open-ephys/shuttle-drive/large_64drives/assembly-jig/50mm_4mm_dowel.SLDPRT

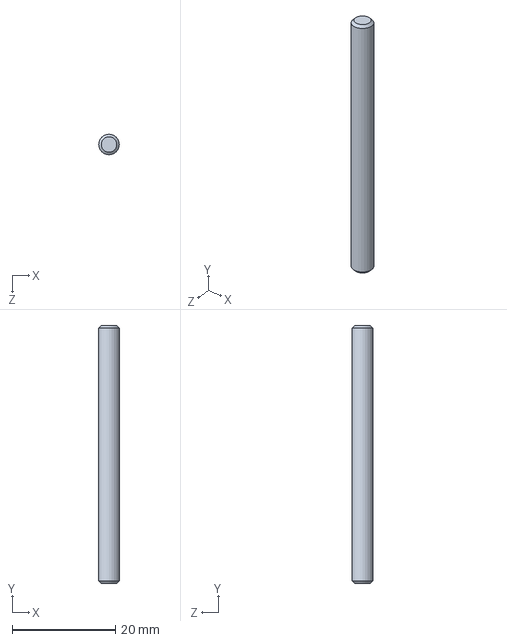
[picture p17: CAD file, 2019-11-18]
large_64drives/assembly-jig/50mm_4mm_dowel.SLDPRT
4.00 x 50.0 x 4.00 mm
