open-ephys/shuttle-drive/large_64drives/CONSMA001-ND.SLDPRT

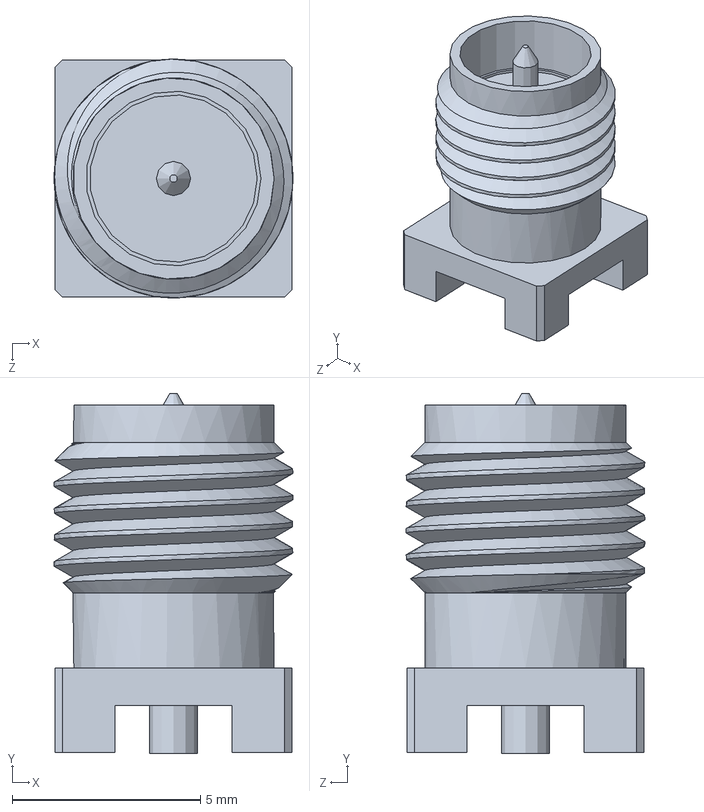
[picture p18: CAD file, 2019-09-19]
large_64drives/CONSMA001-ND.SLDPRT
6.35 x 9.57 x 6.35 mm
