open-ephys/shuttle-drive/small_16drives/assembly_jig/stl_order/low_jig_base_big_rat.STL

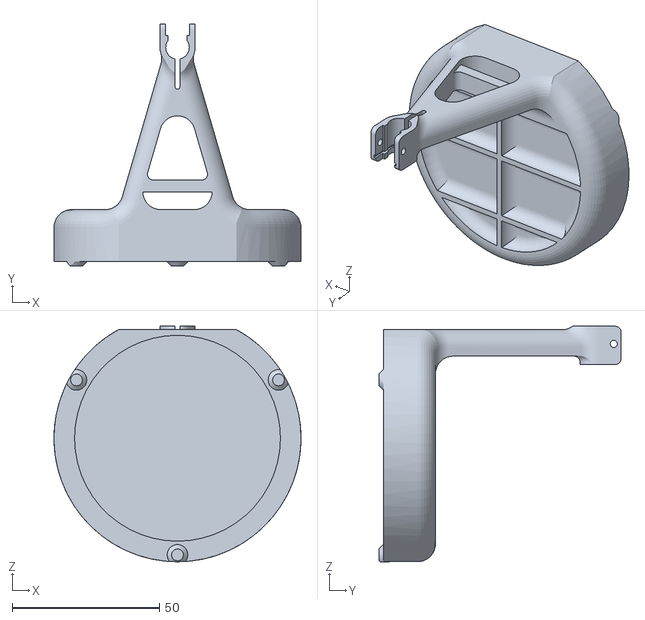
[picture p19: CAD file, 2019-08-24]
small_16drives/assembly_jig/stl_order/low_jig_base_big_rat.STL
83.8 x 82.2 x 79.9
