open-ephys/shuttle-drive/small_16drives/drive_small/drive_shuttle_palletized.SLDPRT

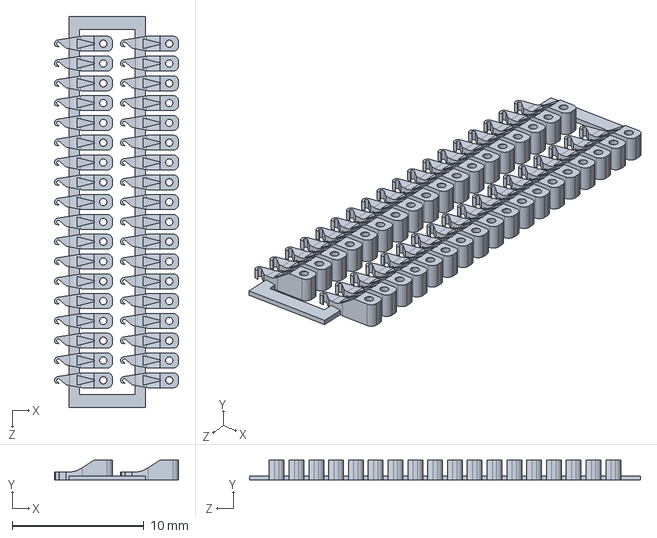
[picture p20: CAD file, 2019-08-24]
small_16drives/drive_small/drive_shuttle_palletized.SLDPRT
9.39 x 1.50 x 29.6 mm
