open-ephys/shuttle-drive/small_16drives/drive_small/not_needed_for_drives/3d_printed_guide_array.SLDPRT

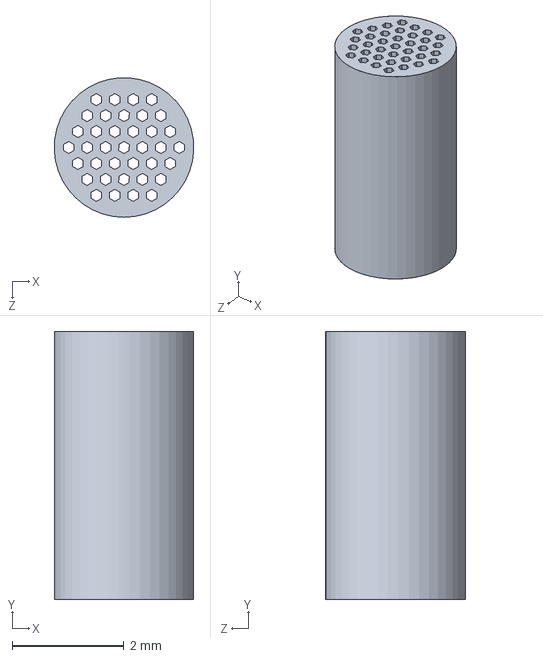
[picture p21: CAD file, 2019-08-24]
small_16drives/drive_small/not_needed_for_drives/3d_printed_guide_array.SLDPRT
2.50 x 4.80 x 2.50 mm
