open-ephys/shuttle-drive/large_64drives/assembly-jig/jig_base_big_rat.SLDPRT

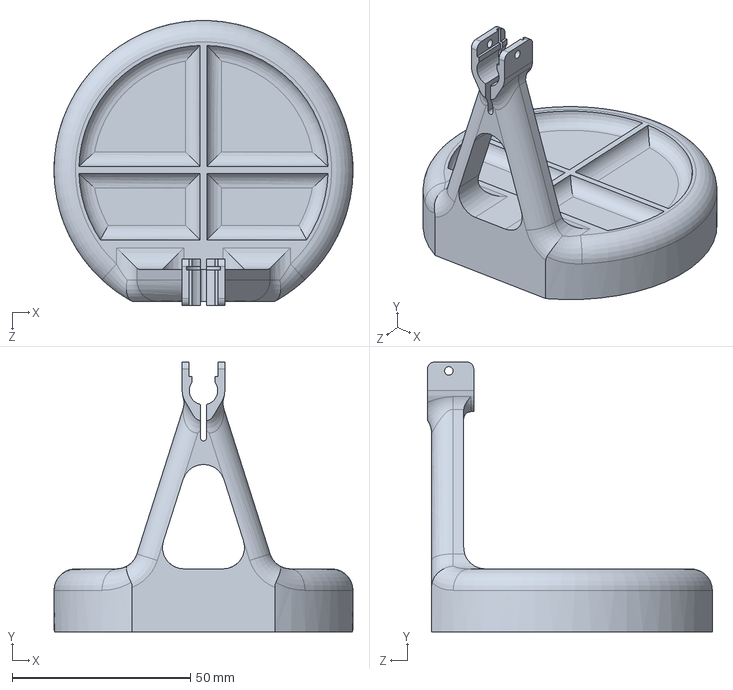
[picture p22: CAD file, 2019-11-18]
large_64drives/assembly-jig/jig_base_big_rat.SLDPRT
83.8 x 75.7 x 79.9 mm
