open-ephys/shuttle-drive/large_64drives/rat_drive_shuttle_short_palletized.SLDPRT

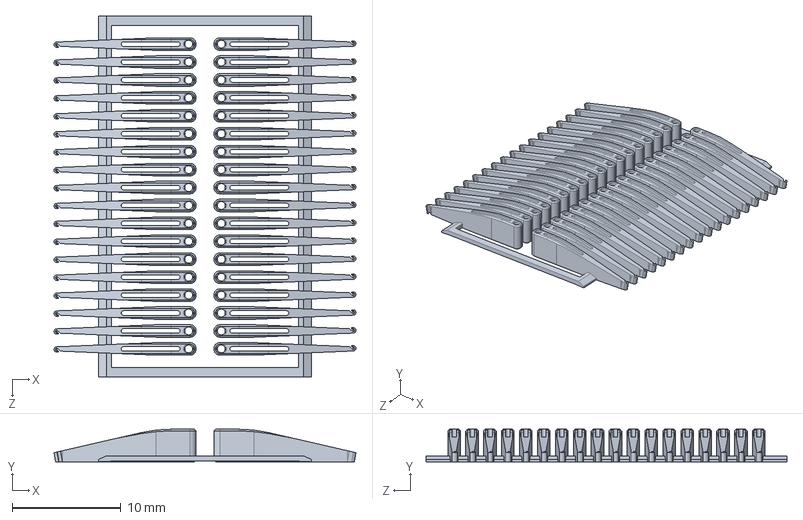
[picture p23: CAD file, 2019-09-19]
large_64drives/rat_drive_shuttle_short_palletized.SLDPRT
27.8 x 3.00 x 33.2 mm
