open-ephys/shuttle-drive/large_64drives/rat_headstage-retainer.sldprt

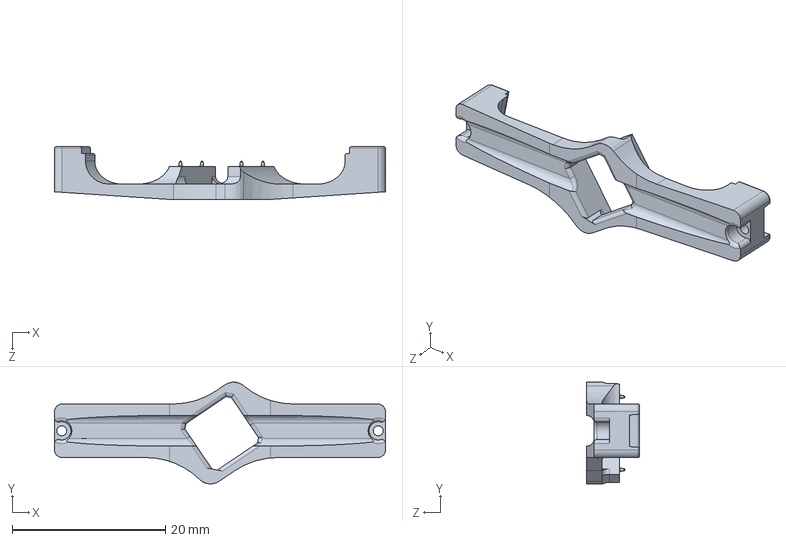
[picture p24: CAD file, 2019-09-19]
large_64drives/rat_headstage-retainer.sldprt
43.2 x 13.3 x 6.90 mm
