open-ephys/shuttle-drive/small_16drives/assembly_jig/stl_order/high_eib_holder_top.STL

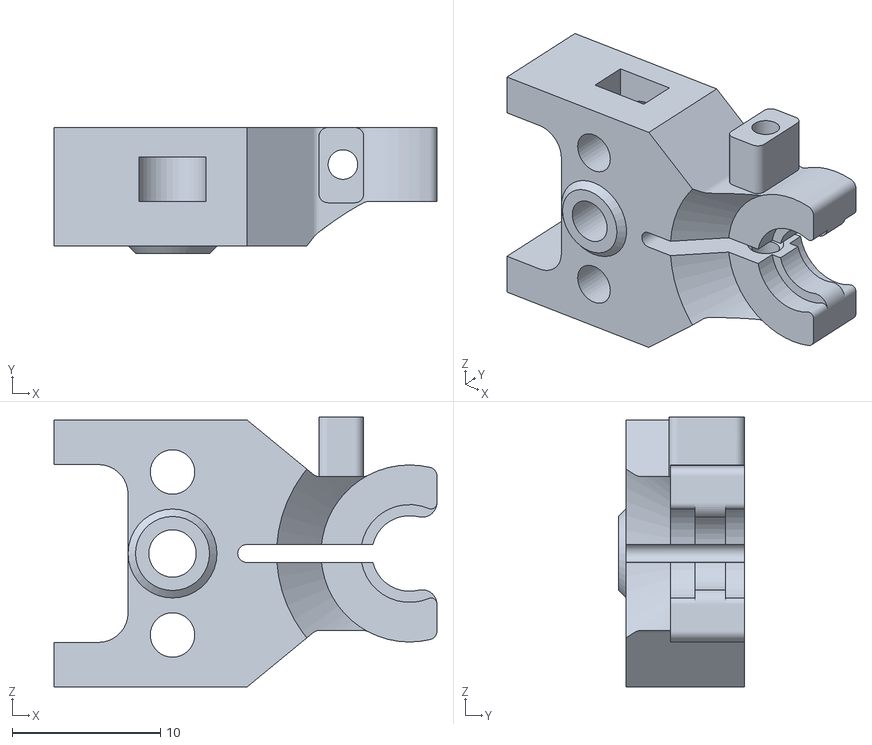
[picture p25: CAD file, 2019-08-24]
small_16drives/assembly_jig/stl_order/high_eib_holder_top.STL
25.9 x 8.50 x 18.2
