open-ephys/shuttle-drive/large_64drives/rat_shuttle_drive_insert_bilateral_vta.SLDPRT

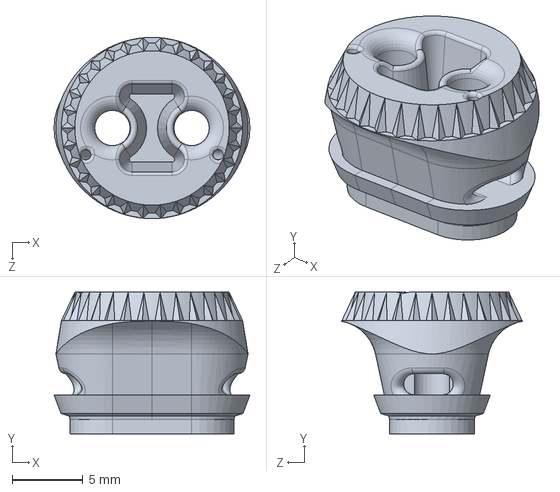
[picture p26: CAD file, 2019-09-19]
large_64drives/rat_shuttle_drive_insert_bilateral_vta.SLDPRT
13.8 x 10.0 x 12.8 mm
