open-ephys/shuttle-drive/small_16drives/assembly_jig/stl_order/high_drive_holder_inner.STL

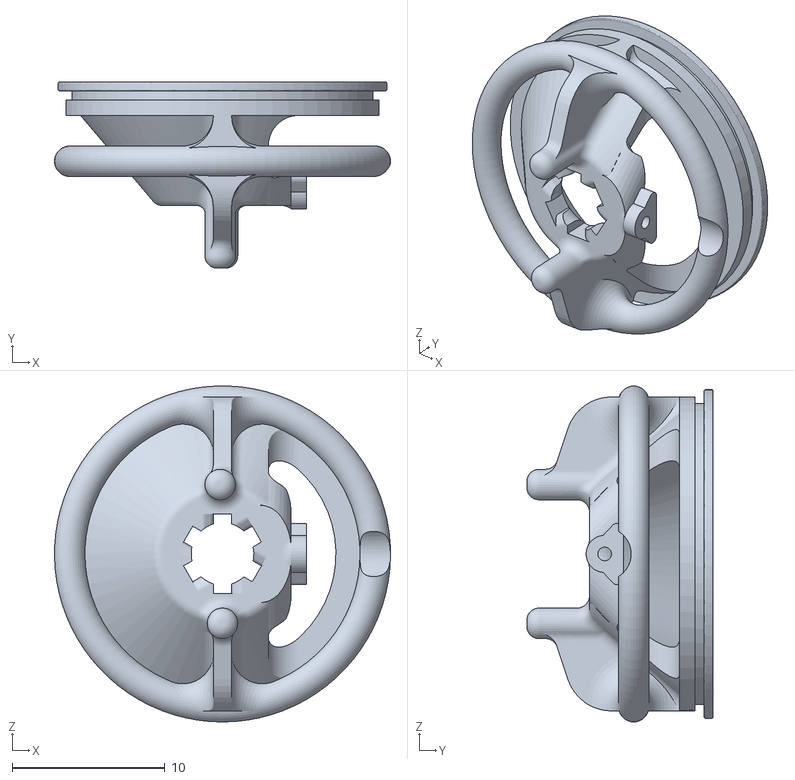
[picture p27: CAD file, 2019-08-24]
small_16drives/assembly_jig/stl_order/high_drive_holder_inner.STL
22.0 x 12.2 x 22.0
