open-ephys/shuttle-drive/large_64drives/rat-eib.SLDPRT

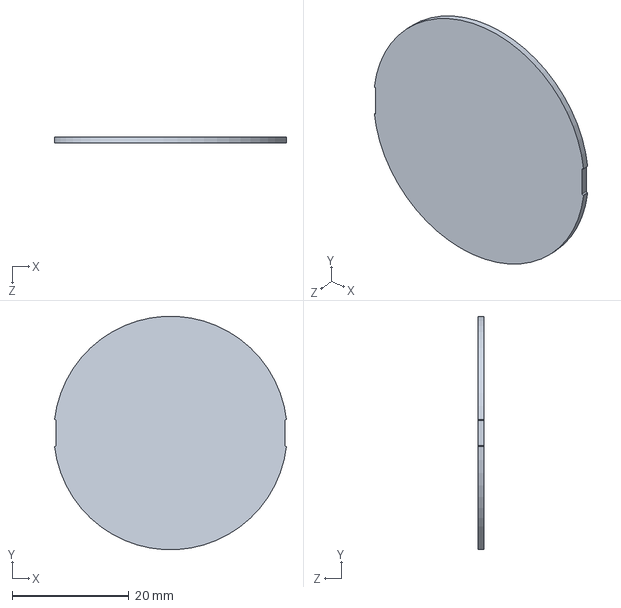
[picture p28: CAD file, 2019-09-19]
large_64drives/rat-eib.SLDPRT
39.7 x 39.9 x 1.00 mm
