open-ephys/shuttle-drive/small_16drives/assembly_jig/stl_order/high_eib_holder_inner_two_omnetics.STL

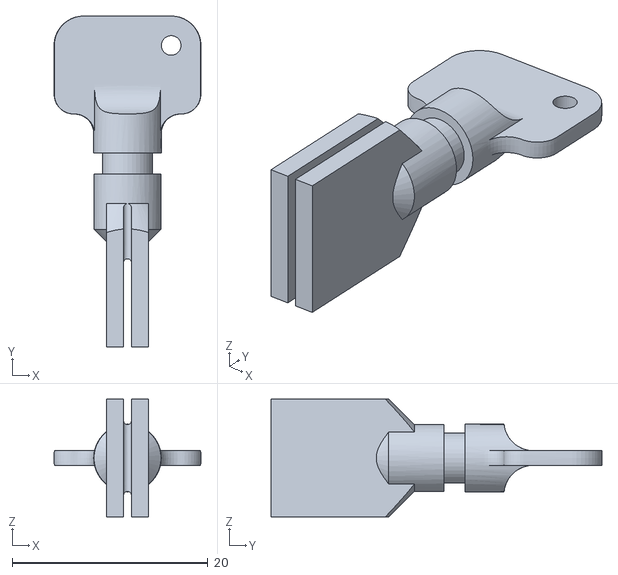
[picture p29: CAD file, 2019-08-24]
small_16drives/assembly_jig/stl_order/high_eib_holder_inner_two_omnetics.STL
15.0 x 33.8 x 12.0
