open-ephys/shuttle-drive/large_64drives/assembly-jig/eib_holder_top.SLDPRT

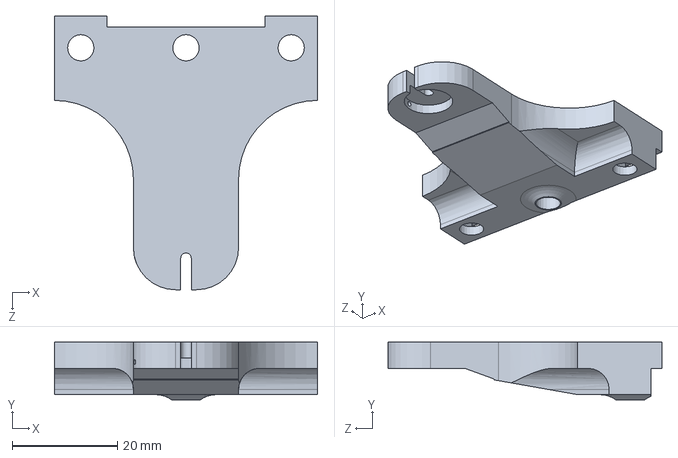
[picture p30: CAD file, 2019-11-18]
large_64drives/assembly-jig/eib_holder_top.SLDPRT
50.0 x 11.0 x 52.0 mm
