open-ephys/shuttle-drive/large_64drives/rat-headstage.SLDPRT

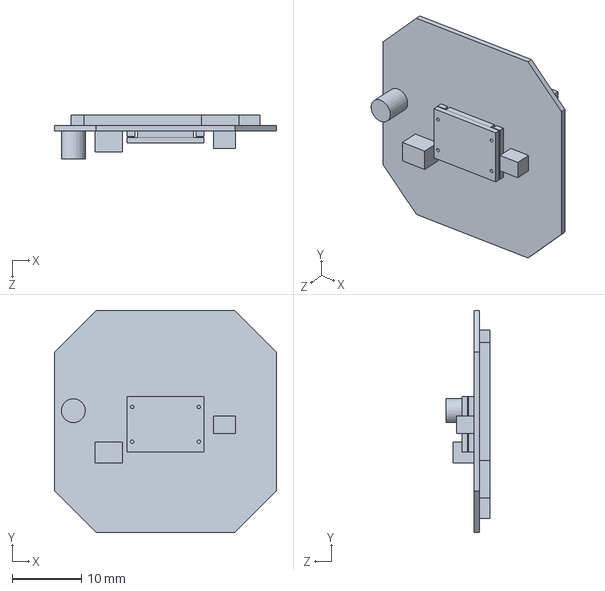
[picture p31: CAD file, 2019-09-19]
large_64drives/rat-headstage.SLDPRT
32.0 x 32.0 x 6.30 mm
