open-ephys/shuttle-drive/large_64drives/assembly-jig/80mm_6mm_dowel.SLDPRT

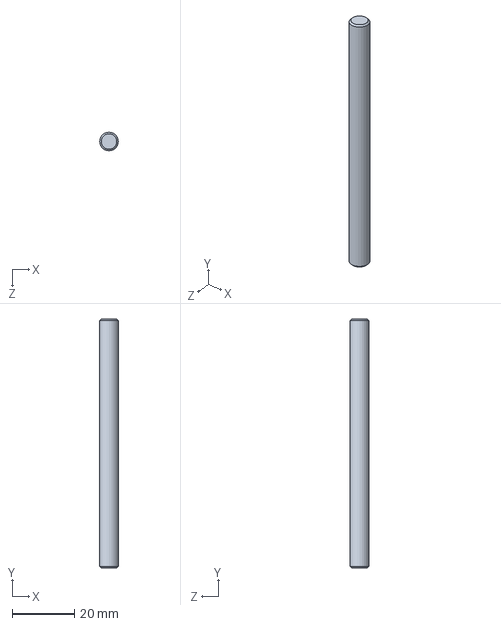
[picture p32: CAD file, 2019-11-18]
large_64drives/assembly-jig/80mm_6mm_dowel.SLDPRT
6.00 x 80.0 x 6.00 mm
