open-ephys/shuttle-drive/small_16drives/assembly_jig/plating_jig_baseSLDPRT.SLDPRT

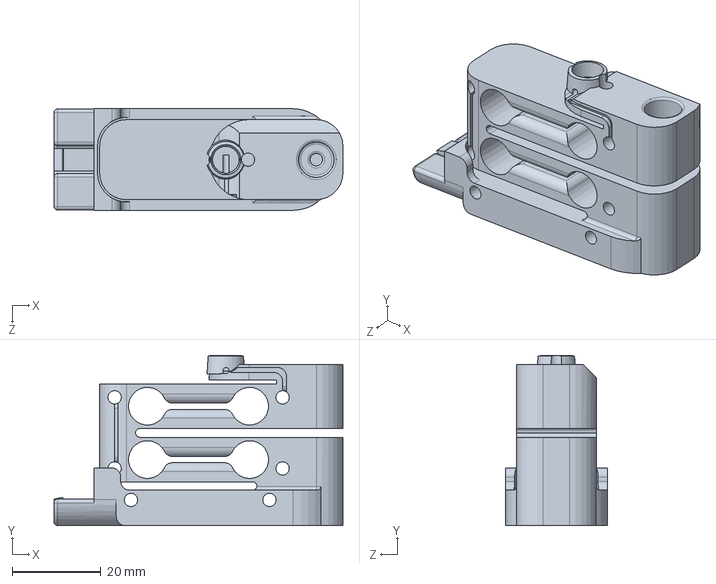
[picture p33: CAD file, 2019-08-24]
small_16drives/assembly_jig/plating_jig_baseSLDPRT.SLDPRT
65.0 x 38.3 x 22.9 mm
