open-ephys/shuttle-drive/small_16drives/assembly_jig/stl_order/high_drive_holder_bottom.STL

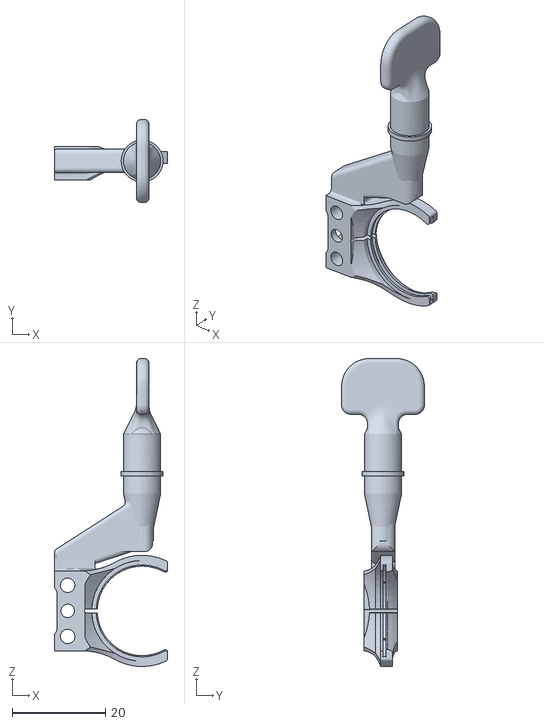
[picture p34: CAD file, 2019-08-24]
small_16drives/assembly_jig/stl_order/high_drive_holder_bottom.STL
24.4 x 17.8 x 66.2
