open-ephys/shuttle-drive/large_64drives/assembly-jig/drive_body_holder_inner_ring.SLDPRT

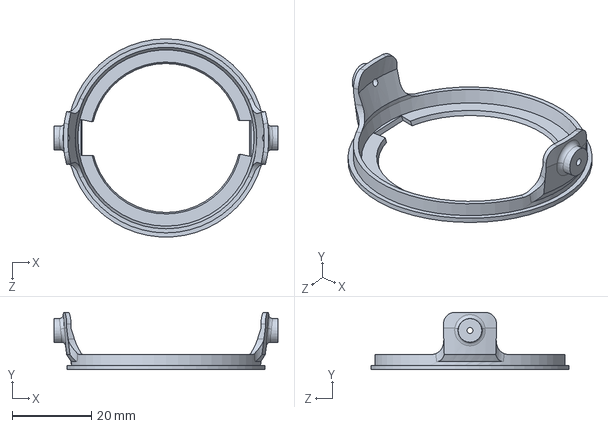
[picture p35: CAD file, 2019-11-18]
large_64drives/assembly-jig/drive_body_holder_inner_ring.SLDPRT
56.5 x 14.5 x 50.0 mm
