open-ephys/shuttle-drive/large_64drives/rat_drive_shuttle_short.SLDPRT

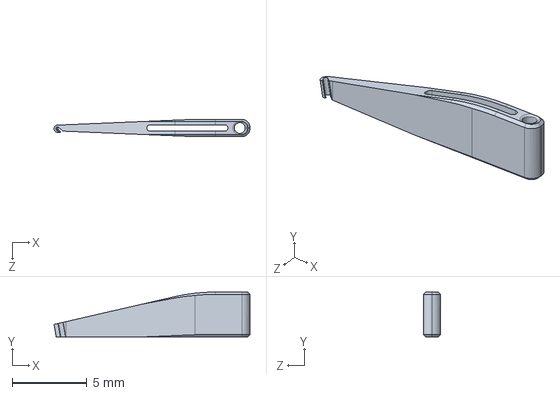
[picture p36: CAD file, 2019-09-19]
large_64drives/rat_drive_shuttle_short.SLDPRT
13.1 x 3.00 x 1.16 mm
