open-ephys/shuttle-drive/small_16drives/assembly_jig/stl_order/high_eib_holder_inner.STL

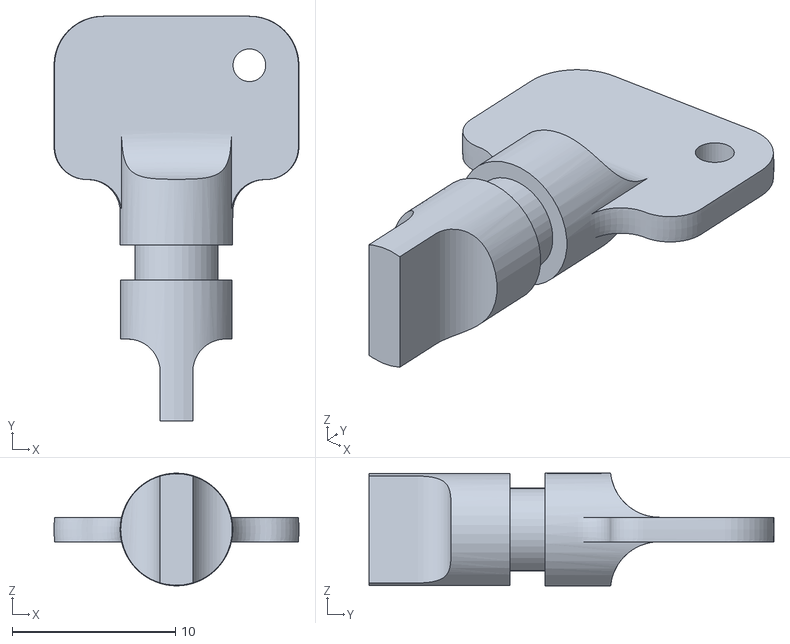
[picture p37: CAD file, 2019-08-24]
small_16drives/assembly_jig/stl_order/high_eib_holder_inner.STL
15.0 x 24.8 x 6.89
