open-ephys/shuttle-drive/large_64drives/assembly-jig/eib_standin.SLDPRT

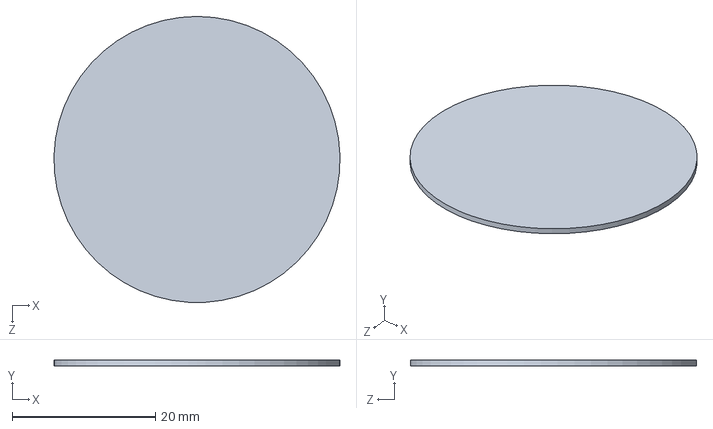
[picture p38: CAD file, 2019-11-18]
large_64drives/assembly-jig/eib_standin.SLDPRT
40.0 x 0.8 x 40.0 mm
