open-ephys/shuttle-drive/large_64drives/assembly-jig/eib256_holder.SLDPRT

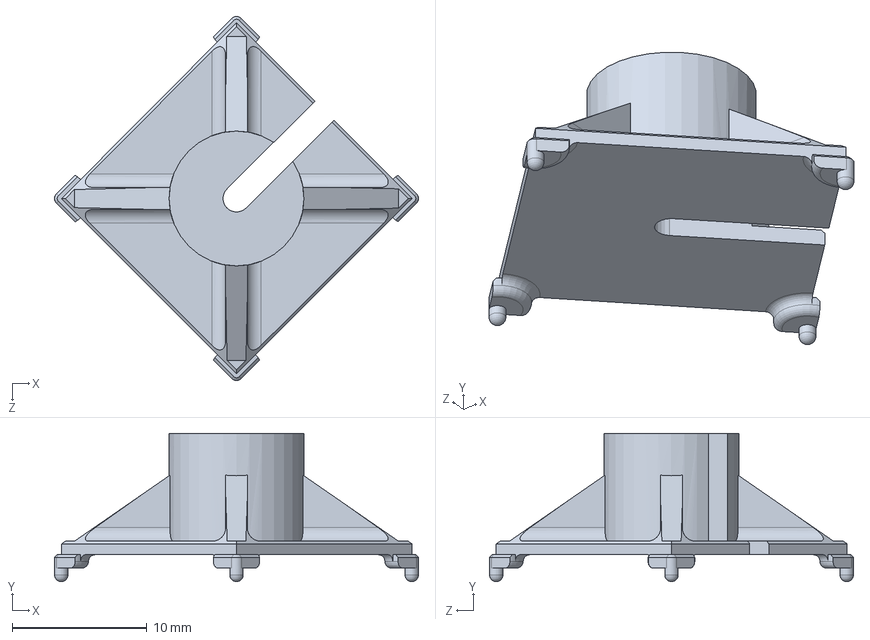
[picture p39: CAD file, 2019-11-18]
large_64drives/assembly-jig/eib256_holder.SLDPRT
27.0 x 11.0 x 27.0 mm
